hongding0211/WeatherStation/Firmware/include/WeatherStationFonts.h

/**The MIT License (MIT)
Copyright (c) 2015 by Daniel Eichhorn
Permission is hereby granted, free of charge, to any person obtaining a copy
of this software and associated documentation files (the "Software"), to deal
in the Software without restriction, including without limitation the rights
to use, copy, modify, merge, publish, distribute, sublicense, and/or sell
copies of the Software, and to permit persons to whom the Software is
furnished to do so, subject to the following conditions:
The above copyright notice and this permission notice shall be included in all
copies or substantial portions of the Software.
THE SOFTWARE IS PROVIDED "AS IS", WITHOUT WARRANTY OF ANY KIND, EXPRESS OR
IMPLIED, INCLUDING BUT NOT LIMITED TO THE WARRANTIES OF MERCHANTABILITY,
FITNESS FOR A PARTICULAR PURPOSE AND NONINFRINGEMENT. IN NO EVENT SHALL THE
AUTHORS OR COPYRIGHT HOLDERS BE LIABLE FOR ANY CLAIM, DAMAGES OR OTHER
LIABILITY, WHETHER IN AN ACTION OF CONTRACT, TORT OR OTHERWISE, ARISING FROM,
OUT OF OR IN CONNECTION WITH THE SOFTWARE OR THE USE OR OTHER DEALINGS IN THE
SOFTWARE.
See more at http://blog.squix.ch
*/

/*
 * https://javl.github.io/image2cpp/
 */
const char custom_lognav_logo [] PROGMEM = {
        0xf7, 0xf7, 0xf3, 0x83, 0xc1, 0xf1, 0xfc, 0xff
};

const char custom_lograindrop [] PROGMEM = {
        0xff, 0xff, 0x87, 0x01, 0x03, 0x8f, 0xff, 0xff
};
const char epd_bitmap_sunrise [] PROGMEM = {
        0xff, 0xff, 0xff, 0x9f, 0x8b, 0x9f, 0xff, 0xff
};
//
const char epd_bitmap_sunset [] PROGMEM = {
        0xff, 0xff, 0xff, 0xbf, 0xf3, 0x9f, 0xff, 0xff
};


const char Meteocons_0_42[] PROGMEM = {
  0x28, // Width: 40
  0x2A, // Height: 42
  0x20, // First Char: 32
  0x5F, // Numbers of Chars: 95

  // Char Widths:
  0x14, // 32: 20
  0x28, // 33: 40
  0x28, // 34: 40
  0x28, // 35: 40
  0x28, // 36: 40
  0x28, // 37: 40
  0x28, // 38: 40
  0x28, // 39: 40
  0x28, // 40: 40
  0x28, // 41: 40
  0x28, // 42: 40
  0x28, // 43: 40
  0x18, // 44: 24
  0x18, // 45: 24
  0x18, // 46: 24
  0x18, // 47: 24
  0x28, // 48: 40
  0x28, // 49: 40
  0x28, // 50: 40
  0x28, // 51: 40
  0x28, // 52: 40
  0x28, // 53: 40
  0x28, // 54: 40
  0x28, // 55: 40
  0x28, // 56: 40
  0x28, // 57: 40
  0x18, // 58: 24
  0x18, // 59: 24
  0x18, // 60: 24
  0x18, // 61: 24
  0x18, // 62: 24
  0x18, // 63: 24
  0x18, // 64: 24
  0x28, // 65: 40
  0x28, // 66: 40
  0x28, // 67: 40
  0x28, // 68: 40
  0x28, // 69: 40
  0x28, // 70: 40
  0x28, // 71: 40
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

  // Font Data:
  0x00,0x00,0x00,0x00,0x00,0x00,0x00,0x00,0x00,0x00,0x00,0x00,0x00,0x00,0x00,0x00,0x00,0x00,0x00,0x00,0x00,0x00,0x00,0x00,0x00,0x00,0x00,0x00,0x00,0x00,0x00,0x00,0x00,0x00,0x00,0x00,0x00,0x00,0x00,0x00,0x00,0x00,0x00,0x00,0x00,0x00,0x00,0x00,0x00,0x00,0x00,0x00,0x00,0x00,0x00,0x00,0x00,0x00,0x00,0x00,0x00,0x00,0x00,0x00,0x00,0x00,0x00,0x00,0x00,0x00,0x00,0x00,0x00,0x00,0x00,0x00,0x00,0x00,0x00,0x00,0x00,0x00,0x00,0x00,0x00,0x00,0x00,0x00,0x00,0x00,0x00,0x00,0x00,0x00,0x00,0x00,0x00,0x00,0x00,0x00,0x00,0x00,0x00,0x00,0x00,0x00, // 32
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
  0x00,0x00,0x00,0x00,0x00,0x00,0x00,0x00,0x00,0x00,0x00,0x06,0x00,0x60,0x00,0x00,0x06,0x00,0xFF,0x07,0xF0,0x7F,0x00,0x8C,0x01,0xC0,0x18,0x00,0xFF,0x07,0xF0,0x7F,0x00,0x73,0x06,0x00,0x06,0x00,0x60,0x00,0x00,0x00,0x00,0x00,0x00,0x00,0x00,0x00,0x00,0x00,0x00,0x00,0x00, // 71
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
};
