hongding0211/WeatherStation/Firmware/include/Debugger.h

#pragma once

#include "ESP8266WiFi.h"

/*
 *
 * Debugger Log
 *
 */

class Debugger {
protected:
    String childName;

    void debuggerLog(String str) {
        Serial.println("[" + childName + "] " + str);
    }
};
