hongding0211/WeatherStation/Firmware/include/SH1106Ui.h

/**The MIT License (MIT)

Copyright (c) 2015 by Fabrice Weinberg

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
Credits for parts of this code go to Daniel Eichhorn
*/

#pragma once

#include <Arduino.h>
#include "SH1106.h"

enum AnimationDirection {
  SLIDE_UP,
  SLIDE_DOWN,
  SLIDE_LEFT,
  SLIDE_RIGHT
};

enum IndicatorPosition {
  TOP,
  RIGHT,
  BOTTOM,
  LEFT
};

enum IndicatorDirection {
  LEFT_RIGHT,
  RIGHT_LEFT
};

enum FrameState {
  IN_TRANSITION,
  FIXED
};

const char ANIMATION_activeSymbole[] PROGMEM = {
  0x00, 0x18, 0x3c, 0x7e, 0x7e, 0x3c, 0x18, 0x00
};

const char ANIMATION_inactiveSymbole[] PROGMEM = {
  0x00, 0x0, 0x0, 0x18, 0x18, 0x0, 0x0, 0x00
};


// Structure of the UiState
struct SH1106UiState {
  int           lastUpdate                = 0;
  int           ticksSinceLastStateSwitch = 0;

  FrameState    frameState                = FIXED;
  int           currentFrame              = 0;
};

typedef bool (*FrameCallback)(SH1106 *display,  SH1106UiState* state, int x, int y);
typedef bool (*OverlayCallback)(SH1106 *display,  SH1106UiState* state);

class SH1106Ui {
  private:
    SH1106             *display;

    // Global dirty flag to indicate that the display needs to be redraw.
    bool                dirty                     = true;

    // Symboles for the Indicator
    IndicatorPosition   indicatorPosition         = BOTTOM;
    IndicatorDirection  indicatorDirection        = LEFT_RIGHT;

    const char*         activeSymbole             = ANIMATION_activeSymbole;
    const char*         inactiveSymbole           = ANIMATION_inactiveSymbole;

    // Values for the Frames
    AnimationDirection  frameAnimationDirection   = SLIDE_RIGHT;

    int                 frameTransitionDirection  = 1;

    int                 ticksPerFrame             = 151; // ~ 5000ms at 30 FPS
    //int                 ticksPerFrame             = 225; // ~ 7000ms at 30 FPS
    int                 ticksPerTransition        = 15;  // ~  500ms at 30 FPS

    bool                autoTransition            = true;

    FrameCallback*      frameFunctions;
    int                 frameCount                = 0;

    // Values for Overlays
    OverlayCallback*    overlayFunctions;
    int                 overlayCount              = 0;

    // UI State
    SH1106UiState      state;

    // Bookeeping for update
    int                 updateInterval            = 33;

    int                 getNextFrameNumber();
    void                drawIndicator();
    void                drawFrame();
    void                drawOverlays();
    void                tick();

  public:

    SH1106Ui(SH1106 *display);

    /**
     * Initialise the display
     */
    void init();

    /**
     * Configure the internal used target FPS
     */
    void setTargetFPS(byte fps);

    // Automatic Controll
    /**
     * Enable automatic transition to next frame after the some time can be configured with `setTimePerFrame` and `setTimePerTransition`.
     */
    void enableAutoTransition();

    /**
     * Disable automatic transition to next frame.
     */
    void disableAutoTransition();

    /**
     * Set the direction if the automatic transitioning
     */
    void setAutoTransitionForwards();
    void setAutoTransitionBackwards();

    /**
     *  Set the approx. time a frame is displayed
     */
    void setTimePerFrame(int time);

    /**
     * Set the approx. time a transition will take
     */
    void setTimePerTransition(int time);

    // Customize indicator position and style
    /**
     * Set the position of the indicator bar.
     */
    void setIndicatorPosition(IndicatorPosition pos);

    /**
     * Set the direction of the indicator bar. Defining the order of frames ASCENDING / DESCENDING
     */
    void setIndicatorDirection(IndicatorDirection dir);

    /**
     * Set the symbole to indicate an active frame in the indicator bar.
     */
    void setActiveSymbole(const char* symbole);

    /**
     * Set the symbole to indicate an inactive frame in the indicator bar.
     */
    void setInactiveSymbole(const char* symbole);

    // Frame settings

    /**
     * Configure what animation is used to transition from one frame to another
     */
    void setFrameAnimation(AnimationDirection dir);

    /**
     * Add frame drawing functions
     */
    void setFrames(FrameCallback* frameFunctions, int frameCount);

    // Overlay

    /**
     * Add overlays drawing functions that are draw independent of the Frames
     */
    void setOverlays(OverlayCallback* overlayFunctions, int overlayCount);

    // Manuell Controll
    void  nextFrame();
    void  previousFrame();

    // State Info
    SH1106UiState getUiState();

    int update();
};
